consolesunleashed/sega-master-system-rgb-encoder-switcher/install-photos/rgb-encoder-switcher-install-04.jpg

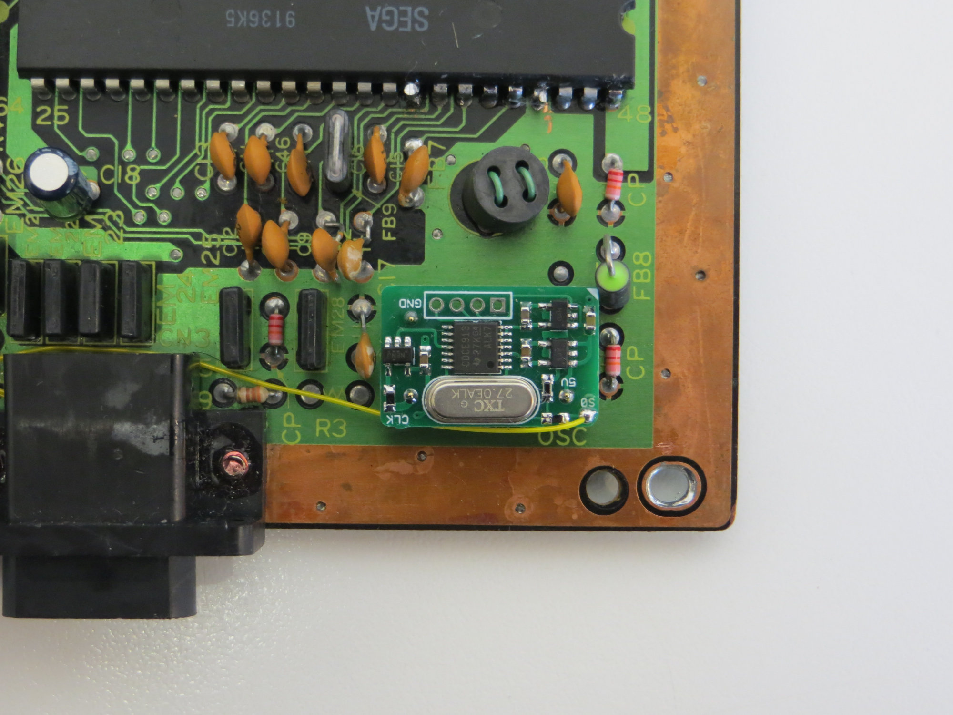
install-photos/rgb-encoder-switcher-install-04.jpg
